TeamPracticalProjects/SISProject/SISHardware/Hub PCB Eagle Files/SIS Hub-sch.pdf

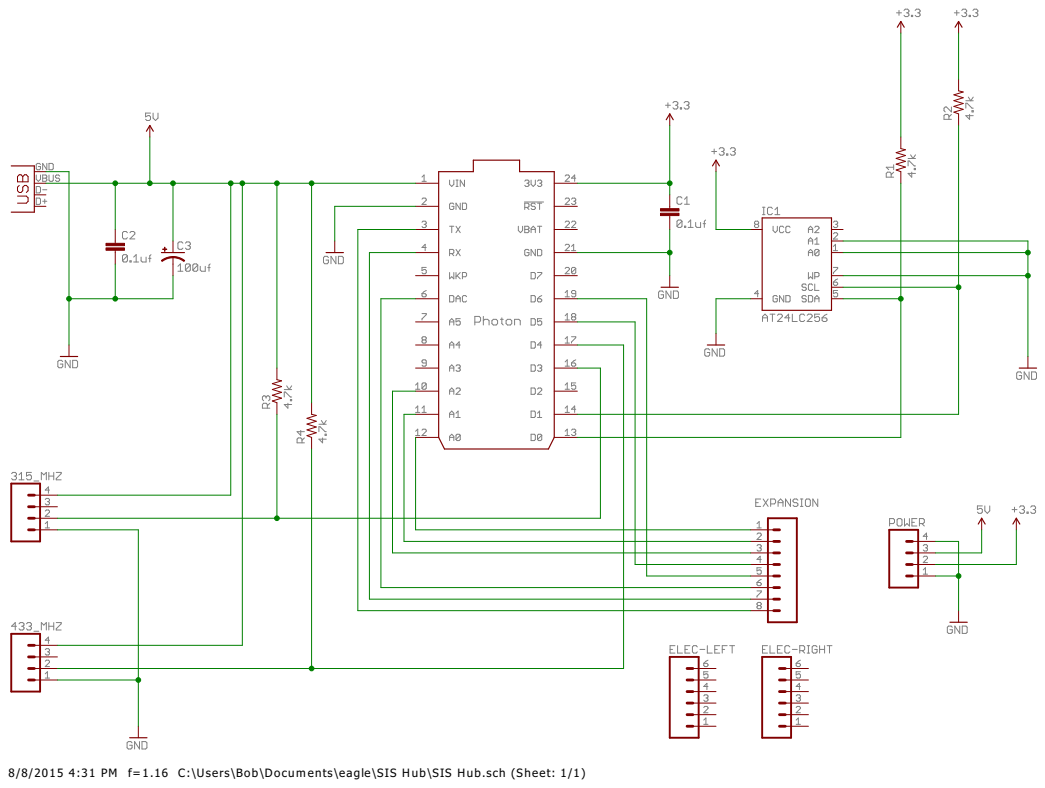
[picture p39: page 1]

8/8/2015 4:31 PM f=1.16 C:\Users\Bob\Documents\eagle\SIS Hub\SIS Hub.sch (Sheet: 1/1)
